nksb92/rlcv2/RLC_V2/RLC_V2.h

#ifndef RLC_V2_H
#define RLC_V2_H

#include "dmx.h"
#include "pdc.h"
#include "leds.h"
#include "rotary_encoder.h"
#include "display.h" 
#include "esp_now.h"
#include "nvm.h"
#include "common.h"

#endif
